fcjr/cubie-a7z-case/images/lid-slim-plain.png

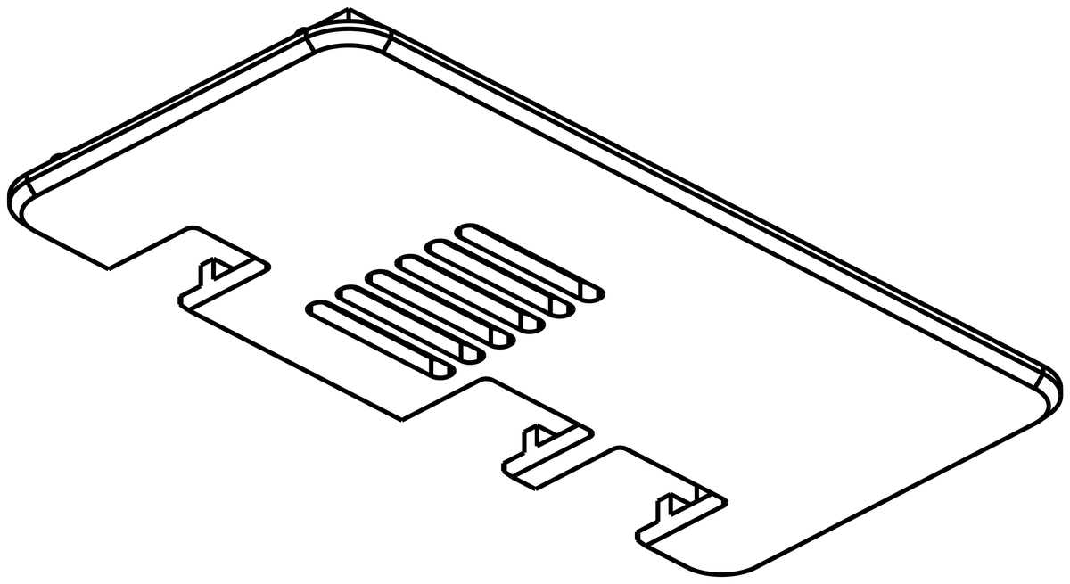
images/lid-slim-plain.png
