fcjr/cubie-a7z-case/images/underside.png

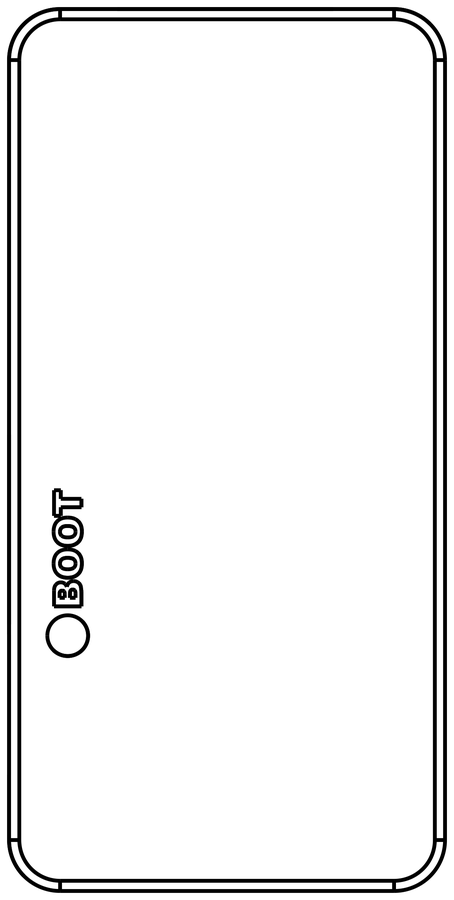
images/underside.png
